GIA-USB/Gialezka/Datasheets/Display/contador1digito.jpg

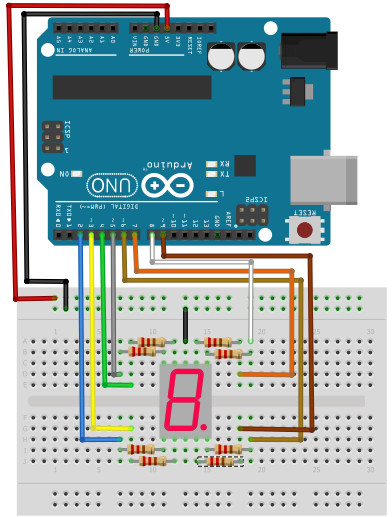
Datasheets/Display/contador1digito.jpg
