GIA-USB/Gialezka/Datasheets/Display/pines_display.jpg

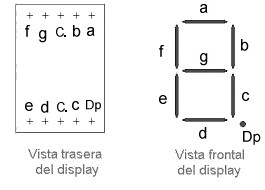
Datasheets/Display/pines_display.jpg
