GIA-USB/Gialezka/Datasheets/UltraSonido/UltraSonido.png

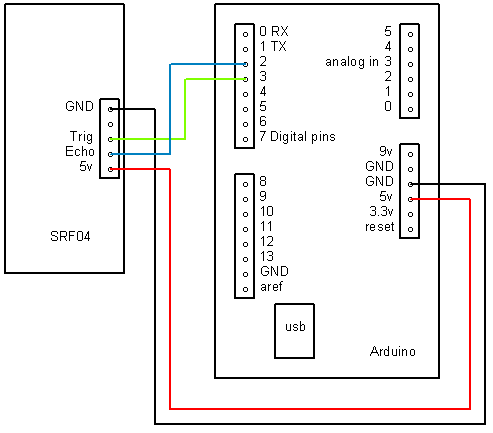
Datasheets/UltraSonido/UltraSonido.png
