GIA-USB/Gialezka/Modelos/1.4(Escala).jpg

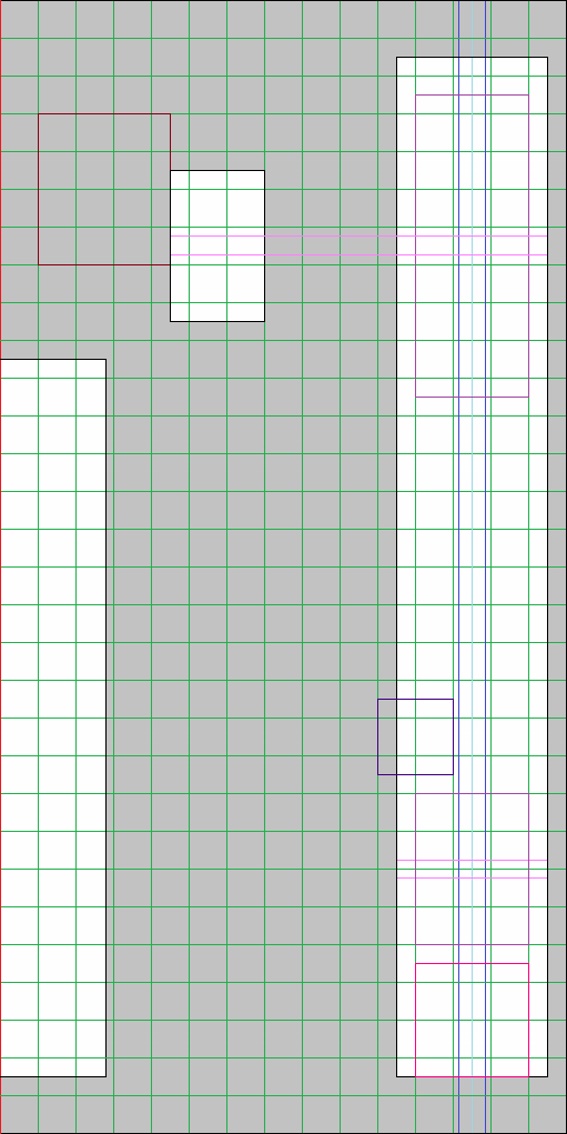
Modelos/1.4(Escala).jpg
