GIA-USB/Gialezka/Datasheets/Display/PrintearDisplay/PrintearDisplay.ino

/*
 LiquidCrystal Library - Hobbytronics
 
 Demonstrates the use a 16x2 LCD display.  The LiquidCrystal
 library works with all LCD displays that are compatible with the 
 Hitachi HD44780 driver. There are many of them out there, and you
 can usually tell them by the 16-pin interface.
 
 This sketch prints "Hobbytronics" to the LCD
 and shows the time.
 This sketch is based on the Arduino sample sketch at 
 http://www.arduino.cc/en/Tutorial/LiquidCrystal
 but with modifications  to the LCD contrast to make it 
 adjustable via software
 
  The circuit:
 * LCD RS pin to digital pin 12
 * LCD Enable pin to digital pin 11
 * LCD R/W pin to Ground 
 * LCD VO pin (pin 3) to PWM pin 9
 * LCD D4 pin to digital pin 5
 * LCD D5 pin to digital pin 4
 * LCD D6 pin to digital pin 3
 * LCD D7 pin to digital pin 2

 */

// include the library code:
#include <LiquidCrystal.h>

// initialize the library with the numbers of the interface pins
LiquidCrystal lcd(12, 11, 5, 4, 3, 2);

void setup() {
  // declare pin 9 to be an output:
  pinMode(9, OUTPUT);  
  analogWrite(9, 50);   
  // set up the LCD's number of columns and rows: 
  lcd.begin(16, 2);
  // Print a message to the LCD.
  lcd.print("  HobbyTronics");
}

void loop() {
  // set the cursor to column 0, line 1
  // (note: line 1 is the second row, since counting begins with 0):
  lcd.setCursor(0, 1);
  // print the number of seconds since reset:
  lcd.print(millis()/1000);
}
